Architeuthis-Flux/Rota/RotaDuck/Graphics/Rotaduck.jpg

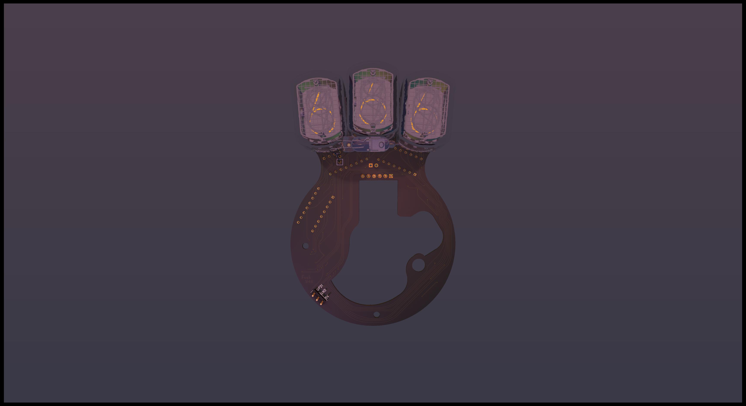
RotaDuck/Graphics/Rotaduck.jpg
