Architeuthis-Flux/Rota/RotaDuck/Graphics/Rotaduck.png

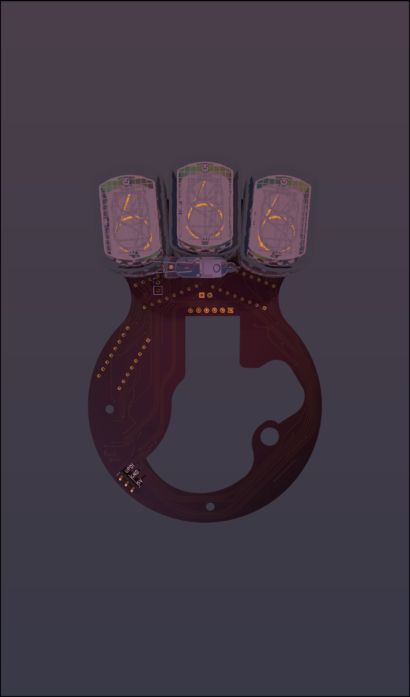
RotaDuck/Graphics/Rotaduck.png
