Architeuthis-Flux/Rota/RotaDuck/Graphics/RotaduckBack.jpg

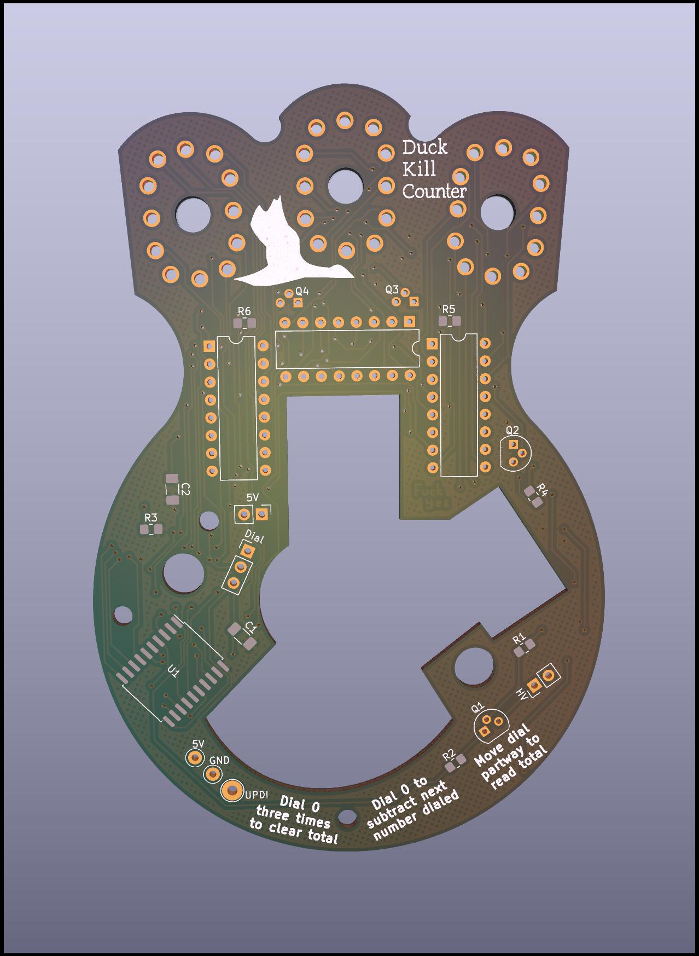
RotaDuck/Graphics/RotaduckBack.jpg
