Architeuthis-Flux/Rota/RotaDuck/Graphics/RotaduckBackskew.jpg

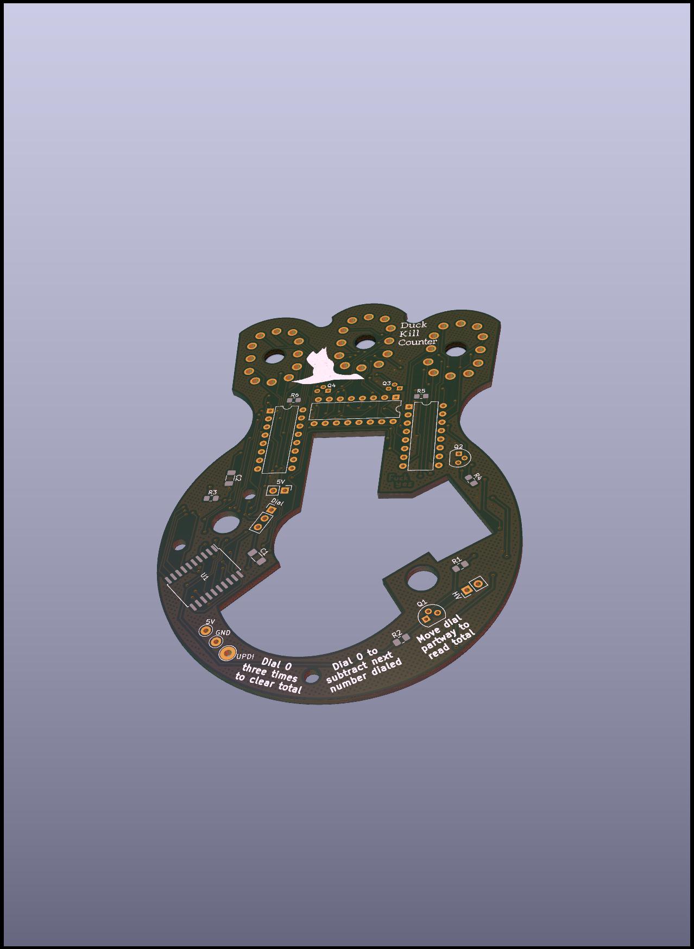
RotaDuck/Graphics/RotaduckBackskew.jpg
