Architeuthis-Flux/Rota/RotaDuck/Graphics/RotaNumberPlate.png

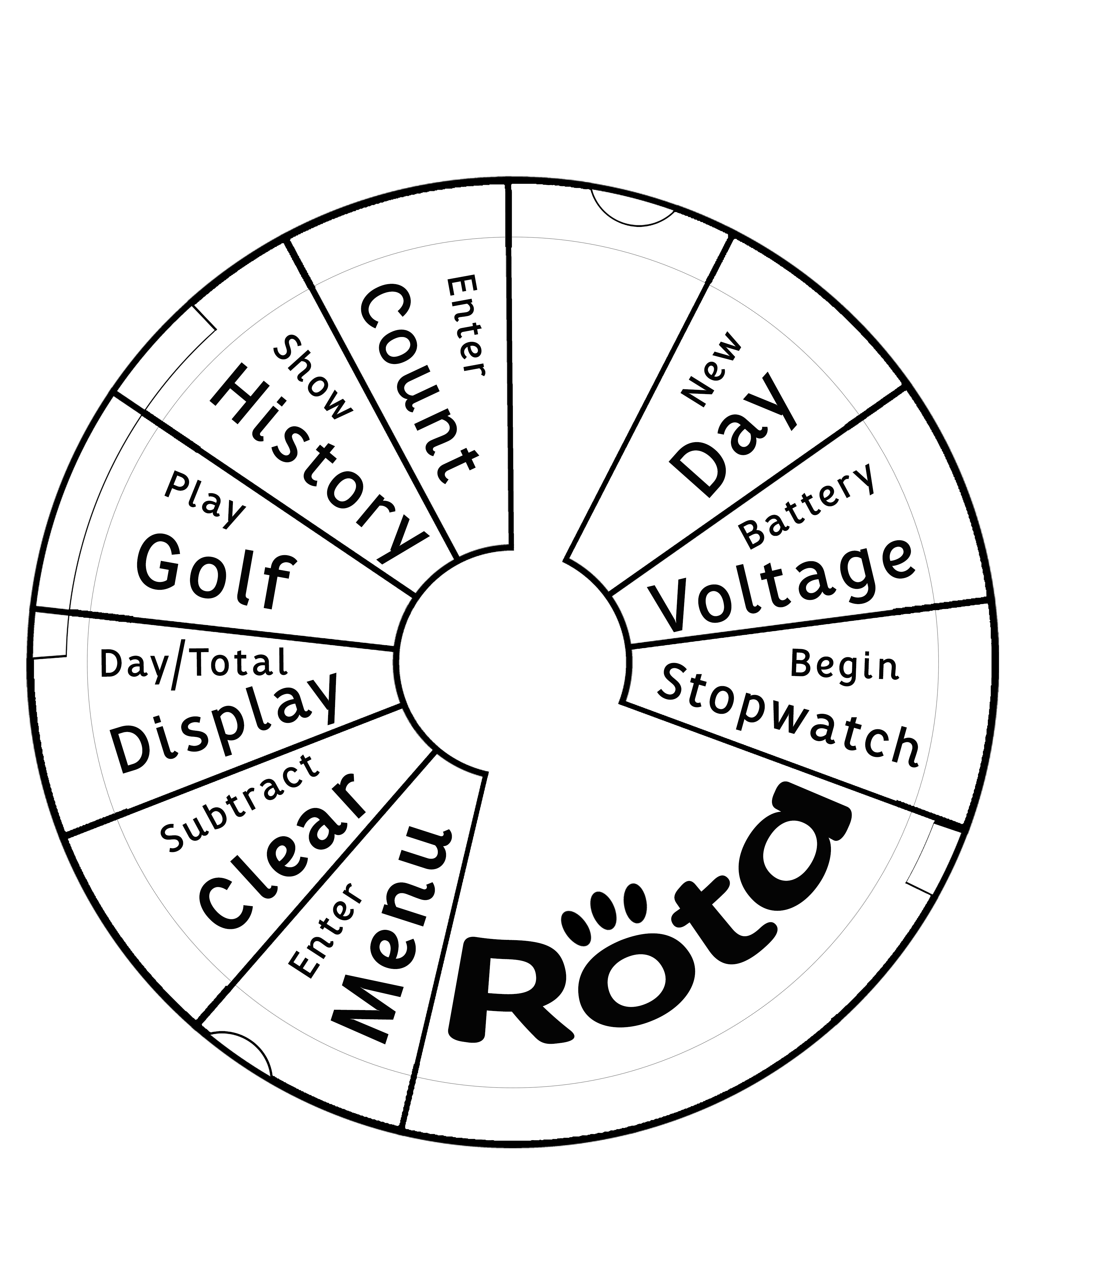
RotaDuck/Graphics/RotaNumberPlate.png
