Architeuthis-Flux/Rota/RotaDuck/Graphics/Screen Shot 2022-01-18 at 9.38.44 AM.png

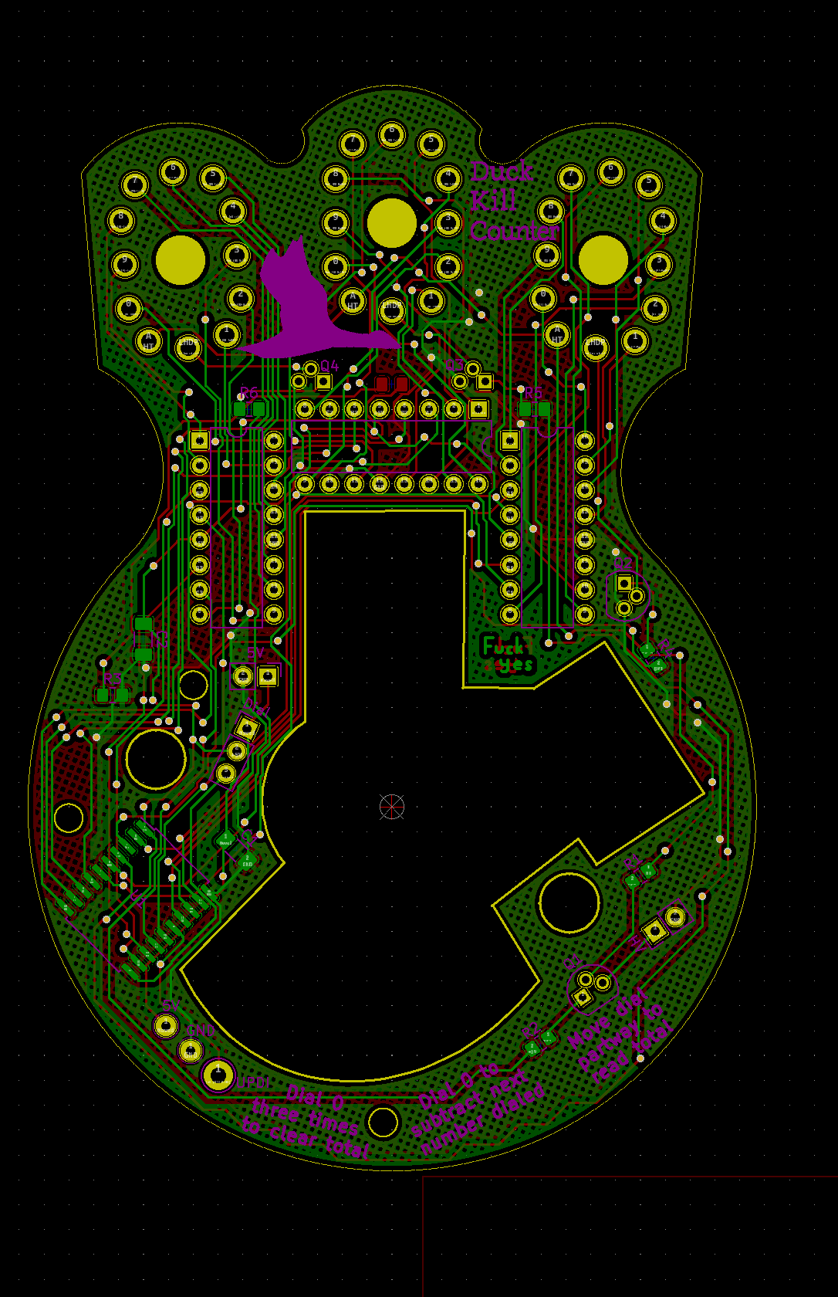
RotaDuck/Graphics/Screen Shot 2022-01-18 at 9.38.44 AM.png
