Architeuthis-Flux/Rota/RotaDuck/Graphics/Screen Shot 2022-06-27 at 10.23.53 AM.jpg

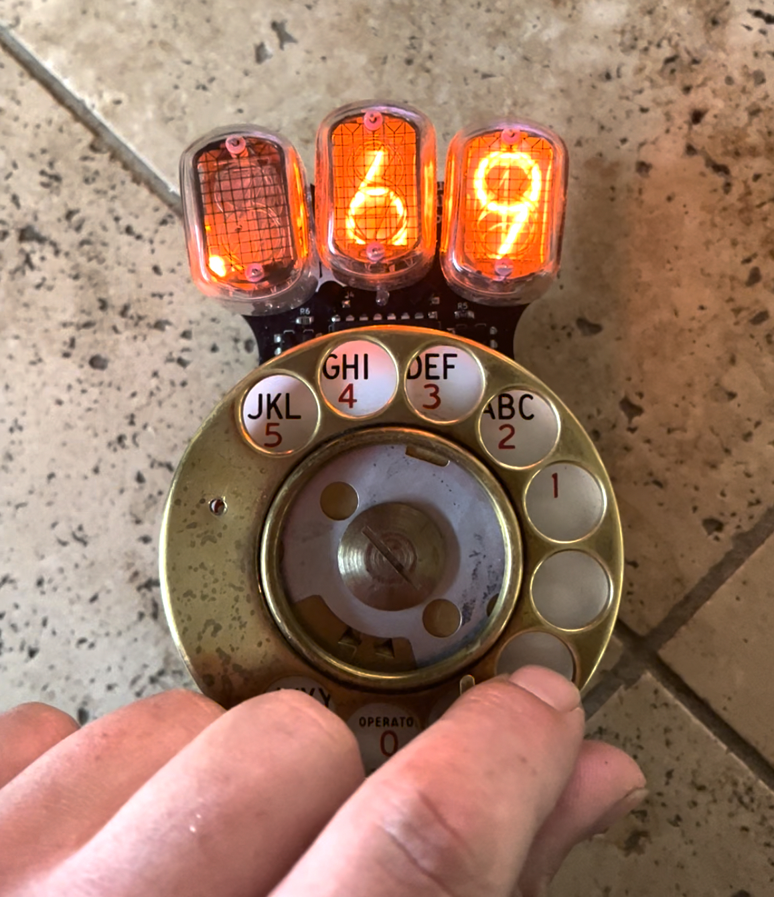
RotaDuck/Graphics/Screen Shot 2022-06-27 at 10.23.53 AM.jpg
