Architeuthis-Flux/Rota/RotaDuck/Graphics/Screen Shot 2022-07-25 at 4.33.00 PM.png

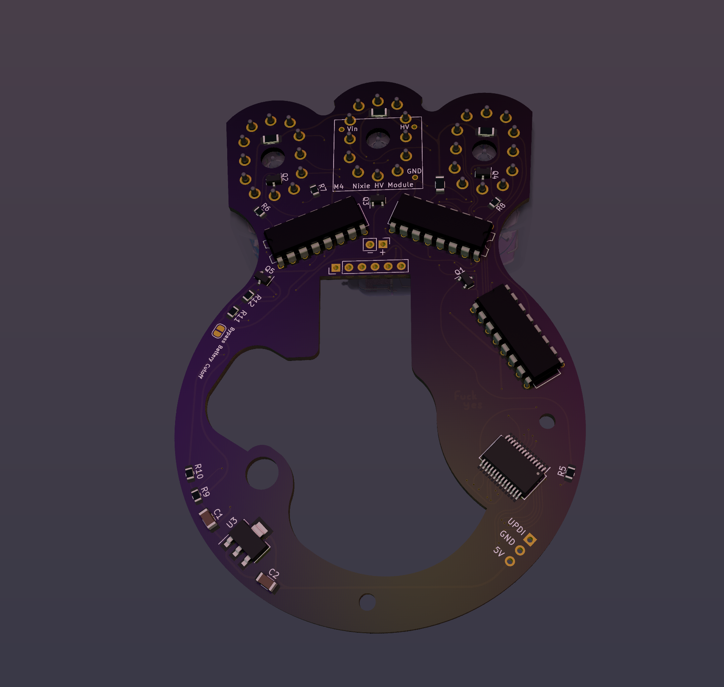
RotaDuck/Graphics/Screen Shot 2022-07-25 at 4.33.00 PM.png
