Architeuthis-Flux/Rota/RotaDuck/Graphics/Screen Shot 2022-07-25 at 5.00.40 PM.png

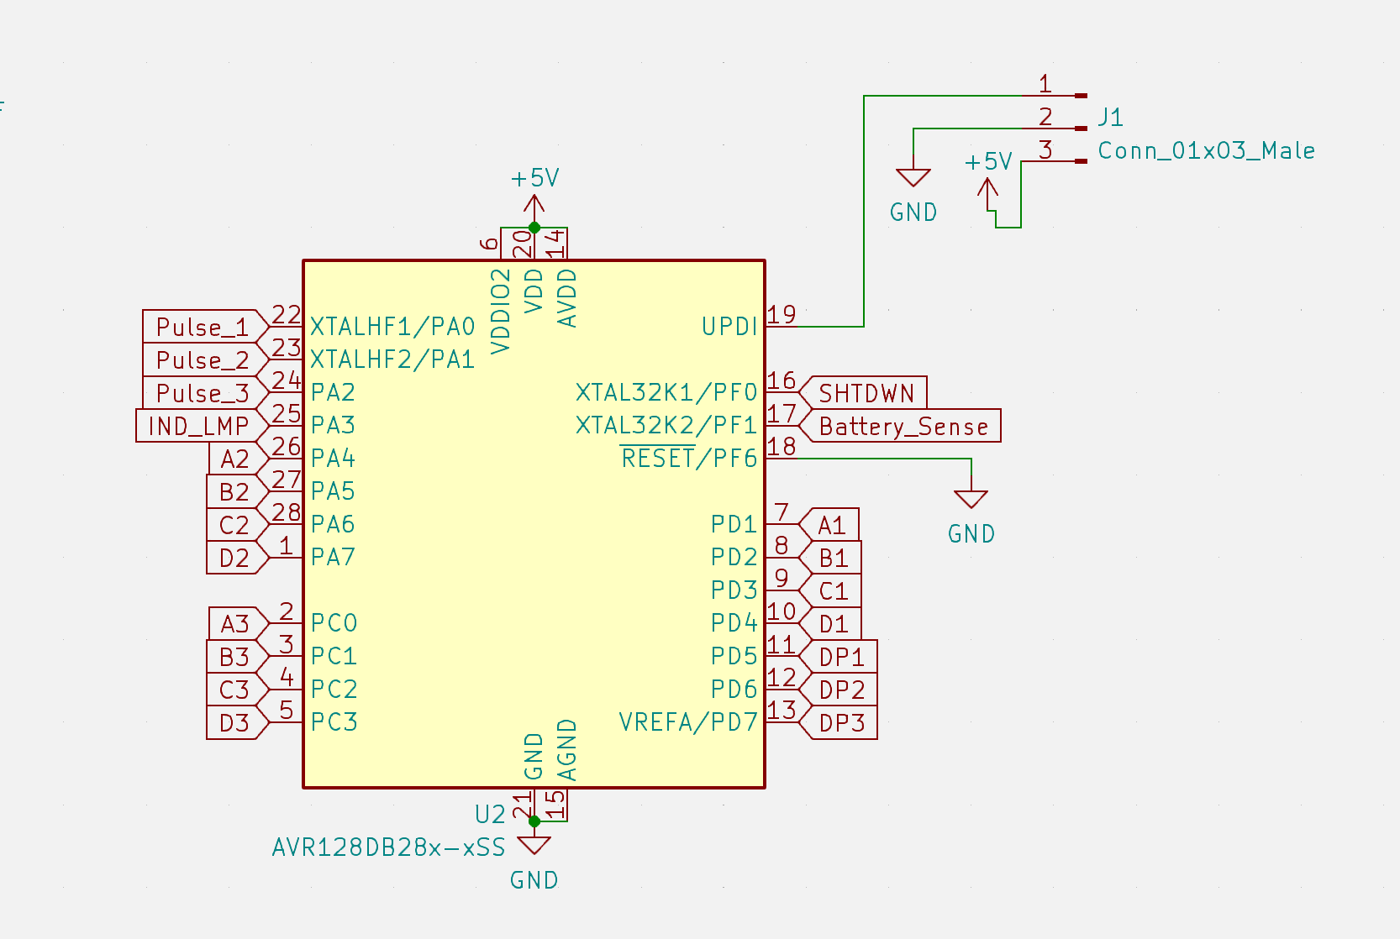
RotaDuck/Graphics/Screen Shot 2022-07-25 at 5.00.40 PM.png
