Architeuthis-Flux/Rota/RotaDuck/Graphics/Screen Shot 2022-07-25 at 9.08.40 AM.png

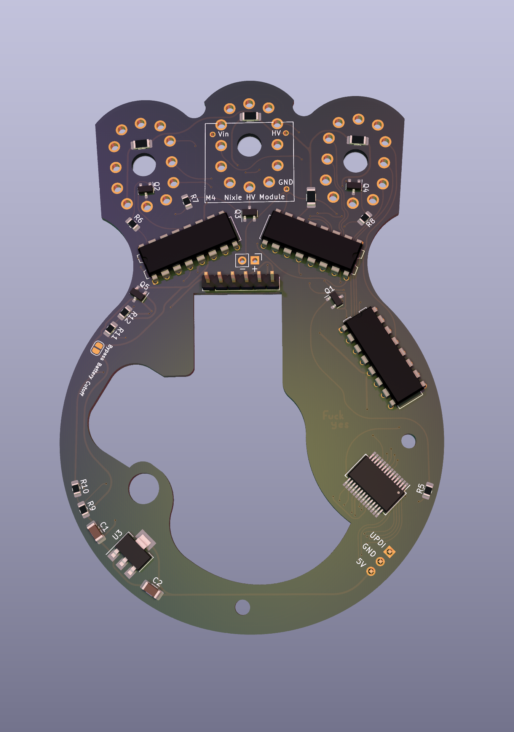
RotaDuck/Graphics/Screen Shot 2022-07-25 at 9.08.40 AM.png
