Architeuthis-Flux/Rota/RotaDuck/Graphics/Untitled 2.jpg

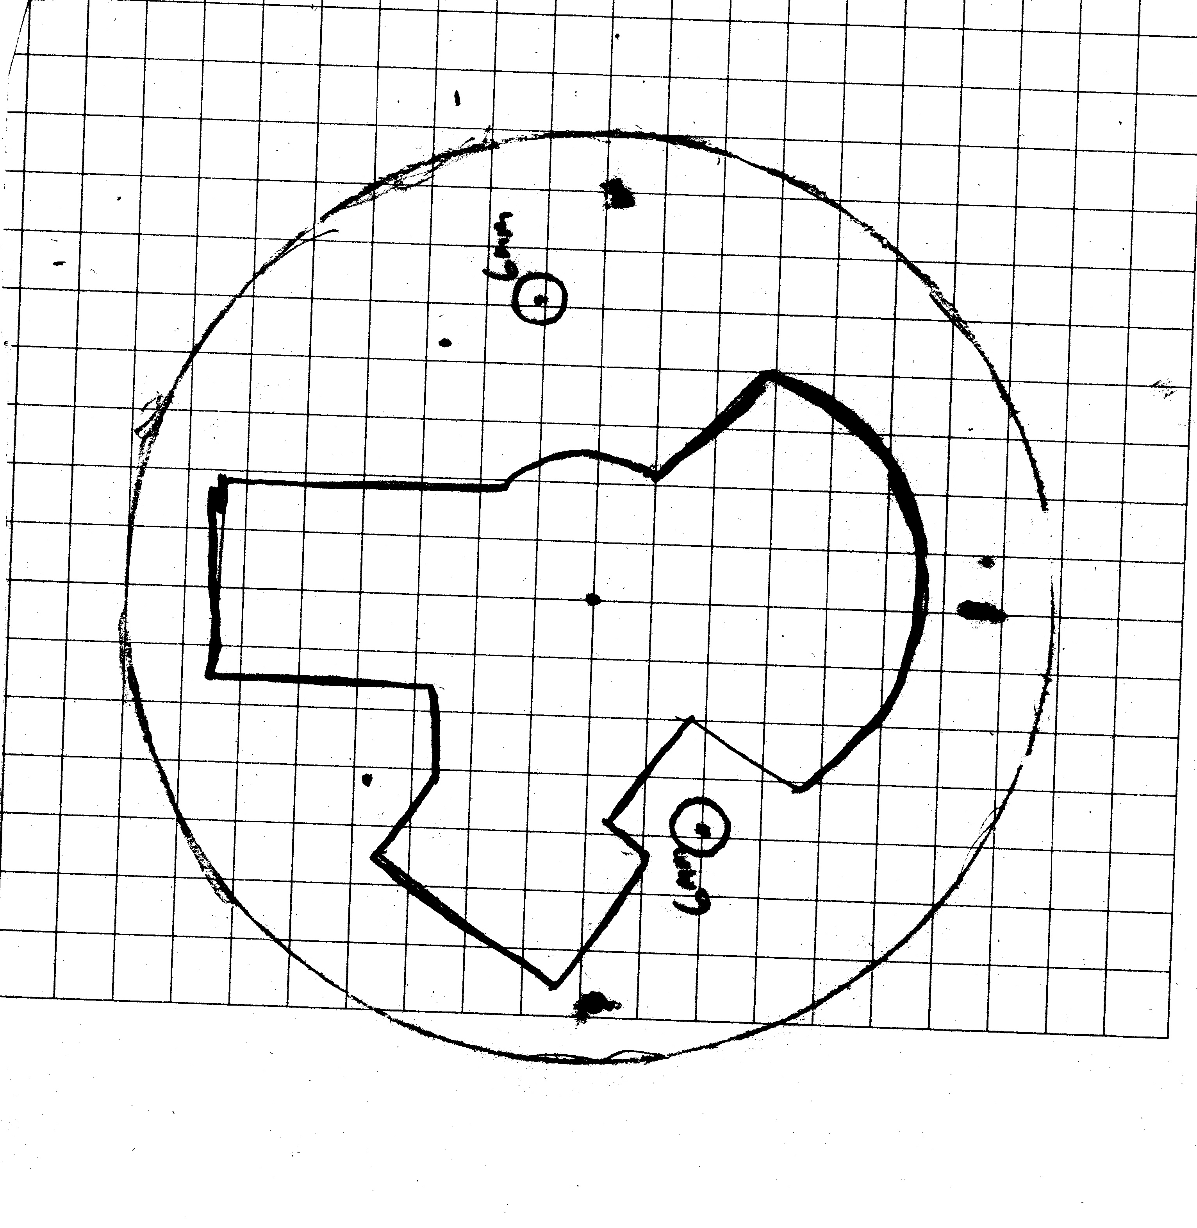
RotaDuck/Graphics/Untitled 2.jpg
