Architeuthis-Flux/Rota/Assembly_Instructions/Pictures/IMG_1347.jpeg

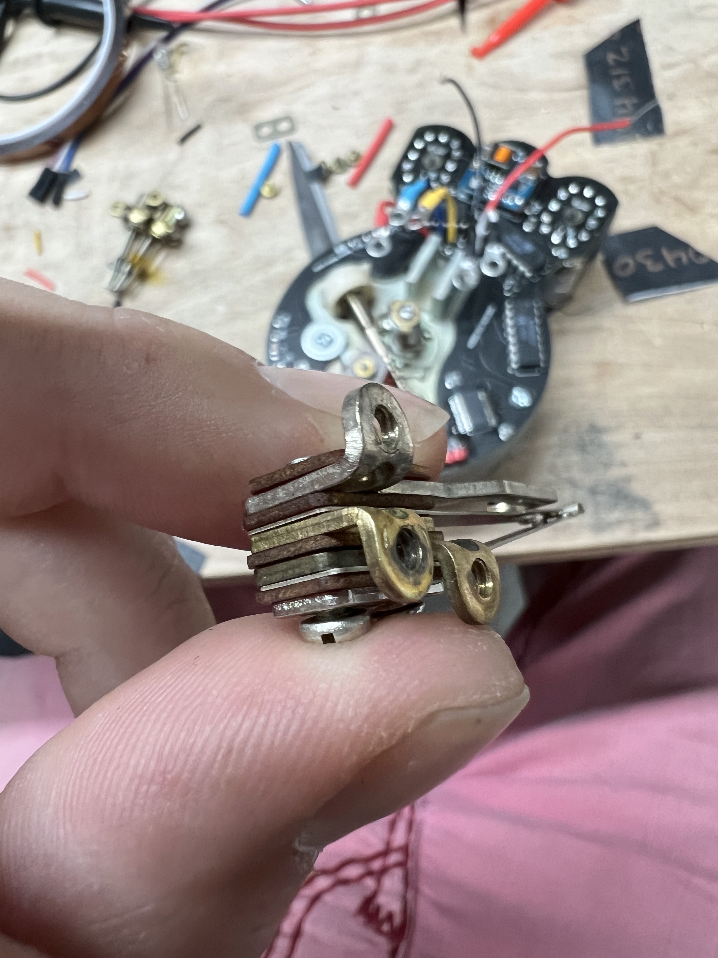
Assembly_Instructions/Pictures/IMG_1347.jpeg
