Architeuthis-Flux/Rota/Assembly_Instructions/Pictures/IMG_1688.jpg

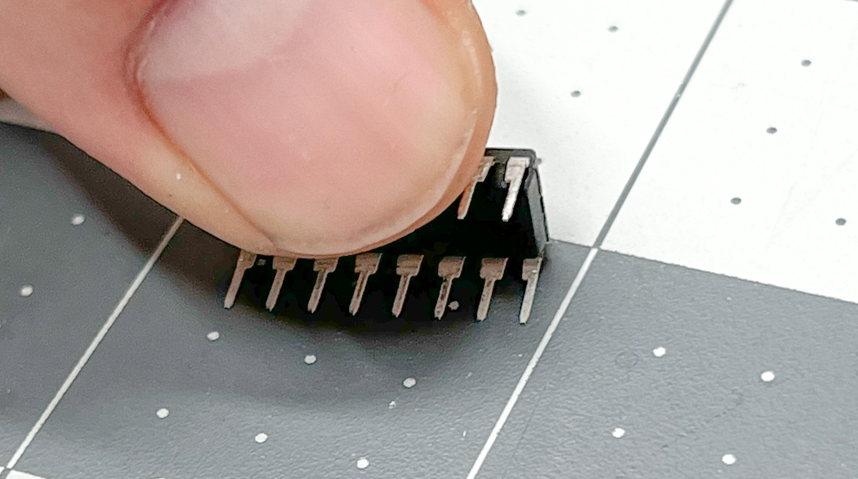
Assembly_Instructions/Pictures/IMG_1688.jpg
