Architeuthis-Flux/Rota/Assembly_Instructions/Pictures/IMG_1715.jpg

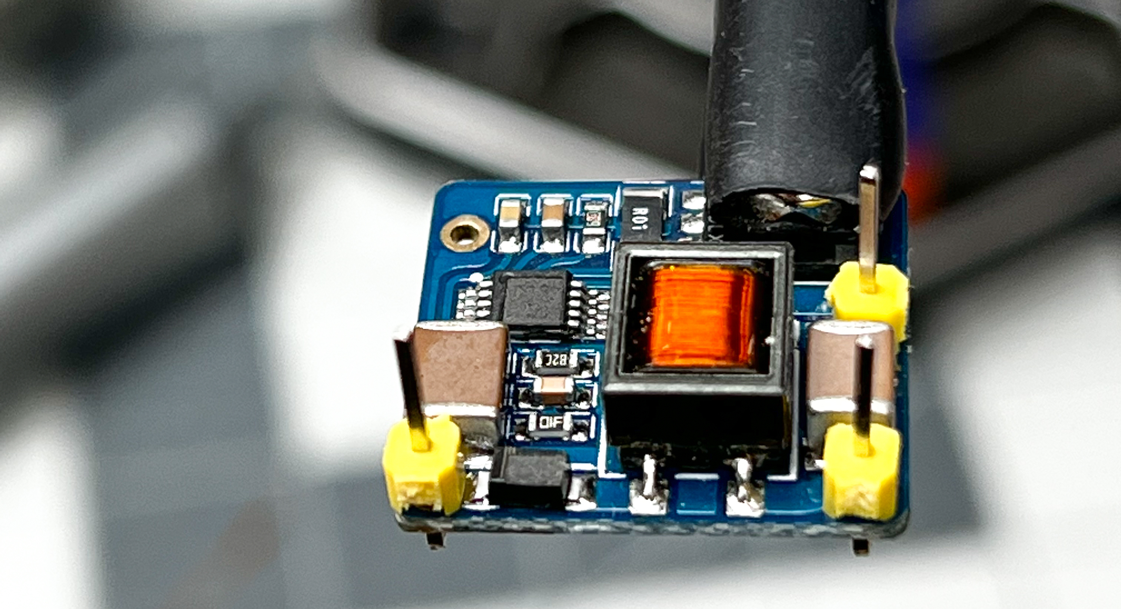
Assembly_Instructions/Pictures/IMG_1715.jpg
