Architeuthis-Flux/Rota/Assembly_Instructions/Pictures/IMG_1725.jpg

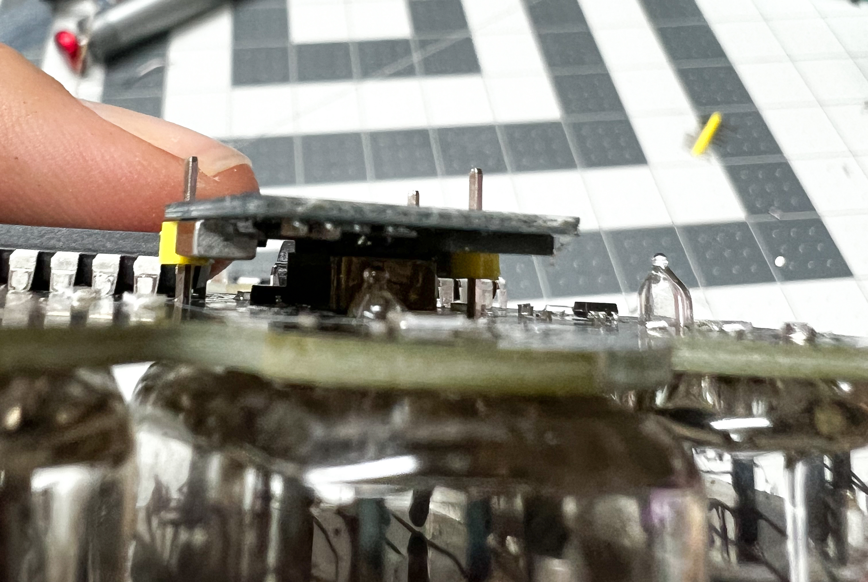
Assembly_Instructions/Pictures/IMG_1725.jpg
