Architeuthis-Flux/Rota/Assembly_Instructions/Pictures/Jumperless-08.jpg

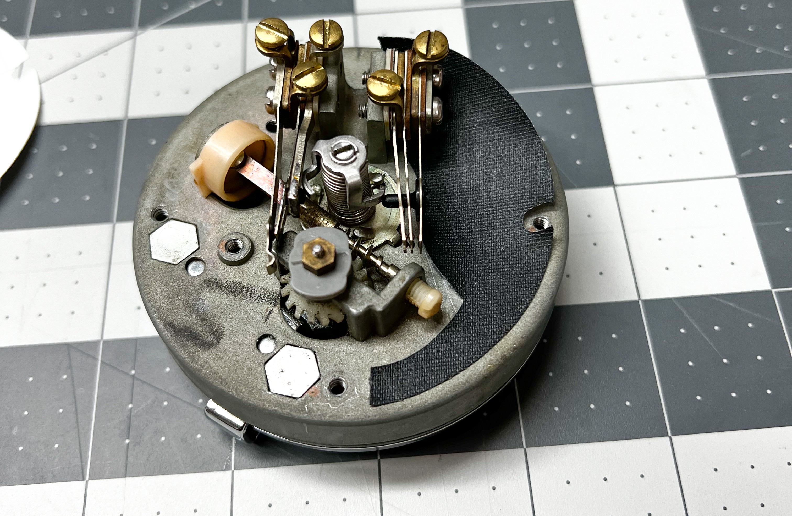
Assembly_Instructions/Pictures/Jumperless-08.jpg
