Architeuthis-Flux/Rota/Assembly_Instructions/Pictures/Jumperless-13.jpg

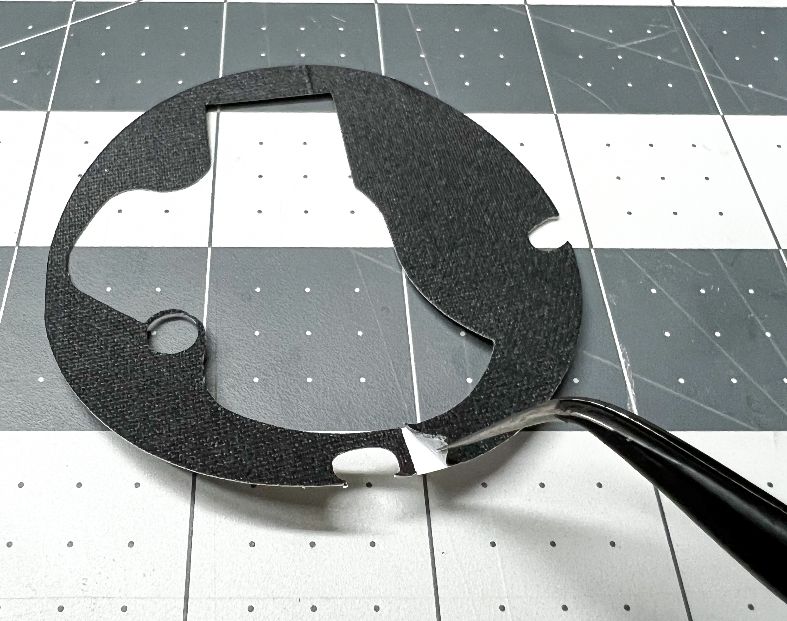
Assembly_Instructions/Pictures/Jumperless-13.jpg
