Architeuthis-Flux/Rota/Assembly_Instructions/Pictures/Jumperless-14.jpg

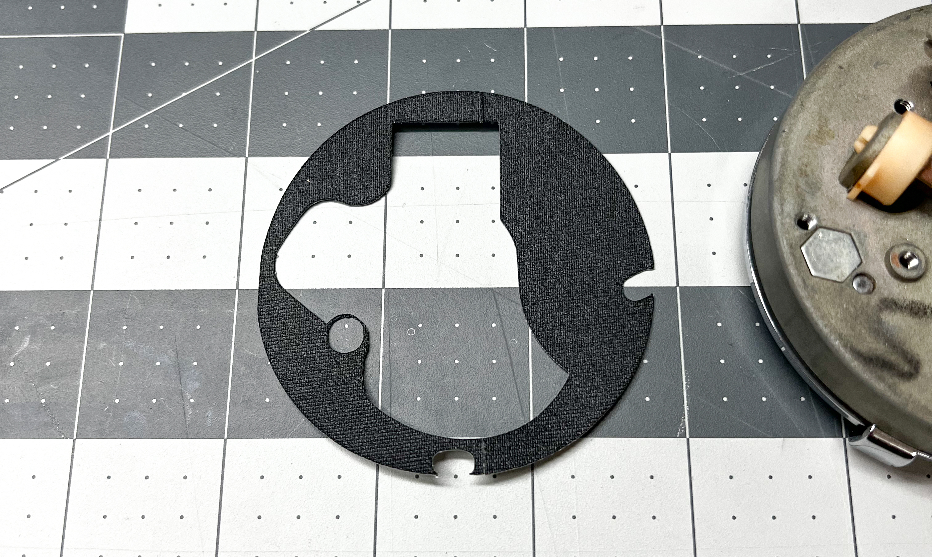
Assembly_Instructions/Pictures/Jumperless-14.jpg
