Architeuthis-Flux/Rota/Assembly_Instructions/Pictures/Jumperless-043.jpeg

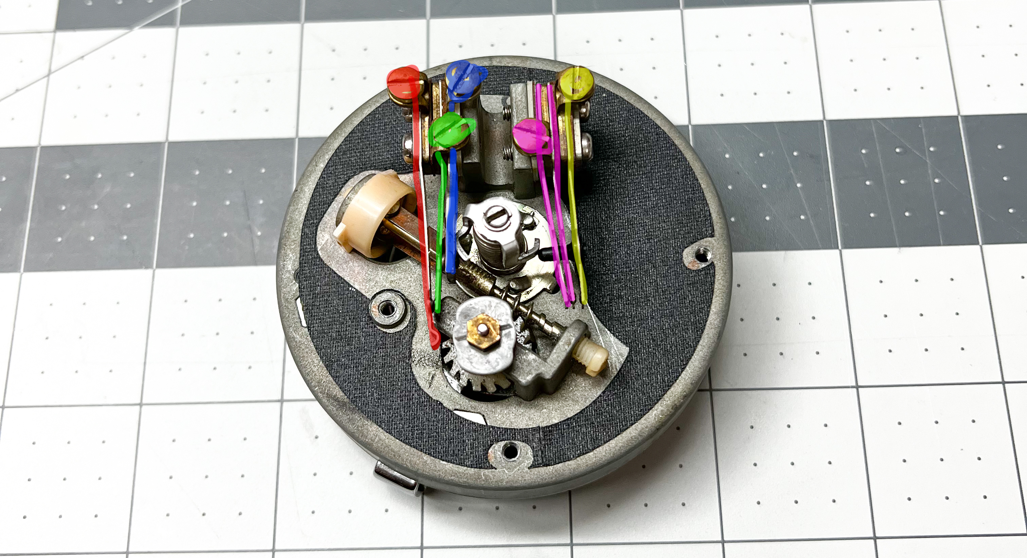
Assembly_Instructions/Pictures/Jumperless-043.jpeg
