Architeuthis-Flux/Rota/Assembly_Instructions/Pictures/SDS00003.png

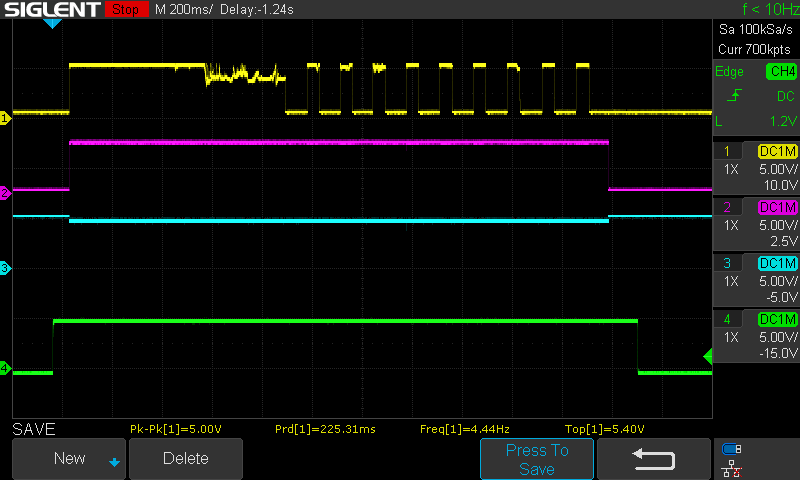
Assembly_Instructions/Pictures/SDS00003.png
