Architeuthis-Flux/Rota/Assembly_Instructions/Pictures/SDS00005.png

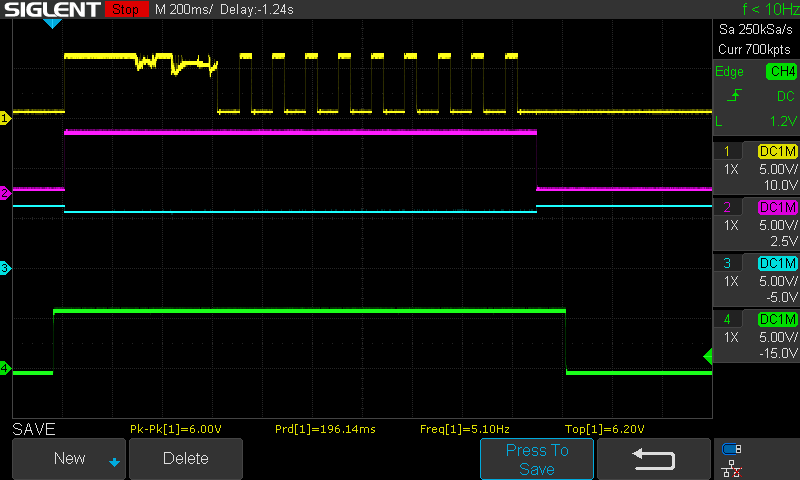
Assembly_Instructions/Pictures/SDS00005.png
