Architeuthis-Flux/Rota/Assembly_Instructions/RotaErrata.jpg

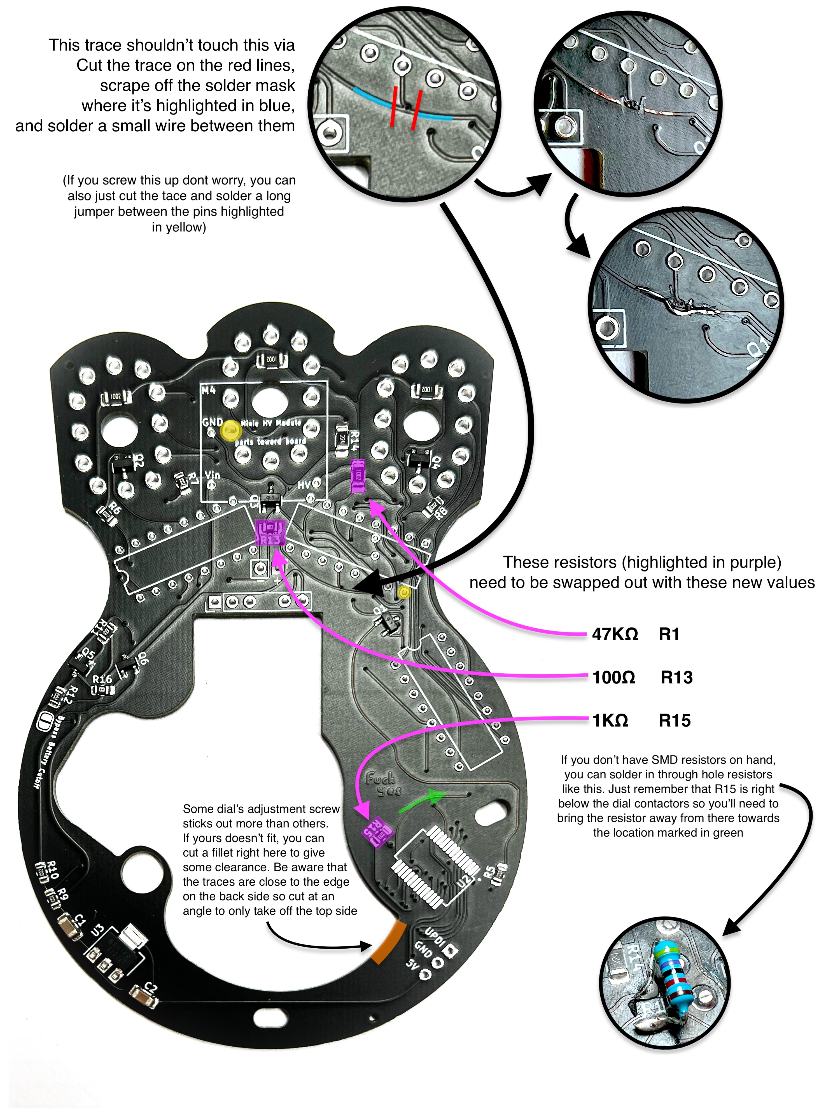
Assembly_Instructions/RotaErrata.jpg
